TendaiRondof/HardwareNeuron/Dokumentation/Perceptron Bsp.docx

# Perceptron Bsp.

x_1 = Input 1

x_2 = input 2

w_1 = gewichtung von input 1

w_2 = gewichtung von input 2

f(x)=1/(1+e^(-x)) = Aktivierungsfunktion

f^(') (x)=(e^(-x))/((1+e^(-x) )^2) = Ableitung der Aktivierungsfunktion

y^(') =Ausgabe des Neurons

Y = Sollausgabe des Neurons

E(y^(') ,Y)=1/2(Y-y')^2 = Error-funktion

Durchlaufsberechnungsformel (Ist beim Training und Benutzen dieselbe (prediction)):

y^(') =f(∑_i x_i *w_i )= f(x_1 *w_1 +x_2 *w_2 )

Bei der Rückrechnung wird zuerst der Fehler (kosten) berechnet:

E(y’,Y)

Dann muss das Delta ( ∆ ) aller w_i berechnet werden, dafür wird die Error Funktion nach den einzelnen w_i abgeleitet:

∆w_i =(∂E(y^(') ,Y))/(∂w_i)

An diesem Punkt wird eine Eigenschaft der Ableitung (Kettenregel) angewendet um dies zu vereinfachen. dafür wird die Errorfunktion einmal nach (Y-y') abgeleitet, was E^(') (y^(') ,Y)= (Y-y') ergibt.

∆w_i =E^(') (y^(') ,Y)*((∂Y)/(∂w_i)-(∂y^('))/(∂w_i))=E^(') (y^(') ,Y)*-(∂y^('))/(∂w_i)=-(Y-y^(') )*(∂y^('))/(∂w_i)

Auf (∂y^('))/(∂w_i) kann nochmals die Kettenregel angewendet werden.

(∂y^('))/(∂w_i)=f^(') (x_i *w_i )*(∂)/(∂w_i)(x_i *w_i )=f^(') (x_i *w_i )*x_i

Das heisst die gesamte Formel ist:

∆w_i =-(Y-y^(') )*f^(') (x_i *w_i )*x_i
